KaiPereira/SODIMM-CM5-Carrier/journal/Pasted image 20250924064620.png

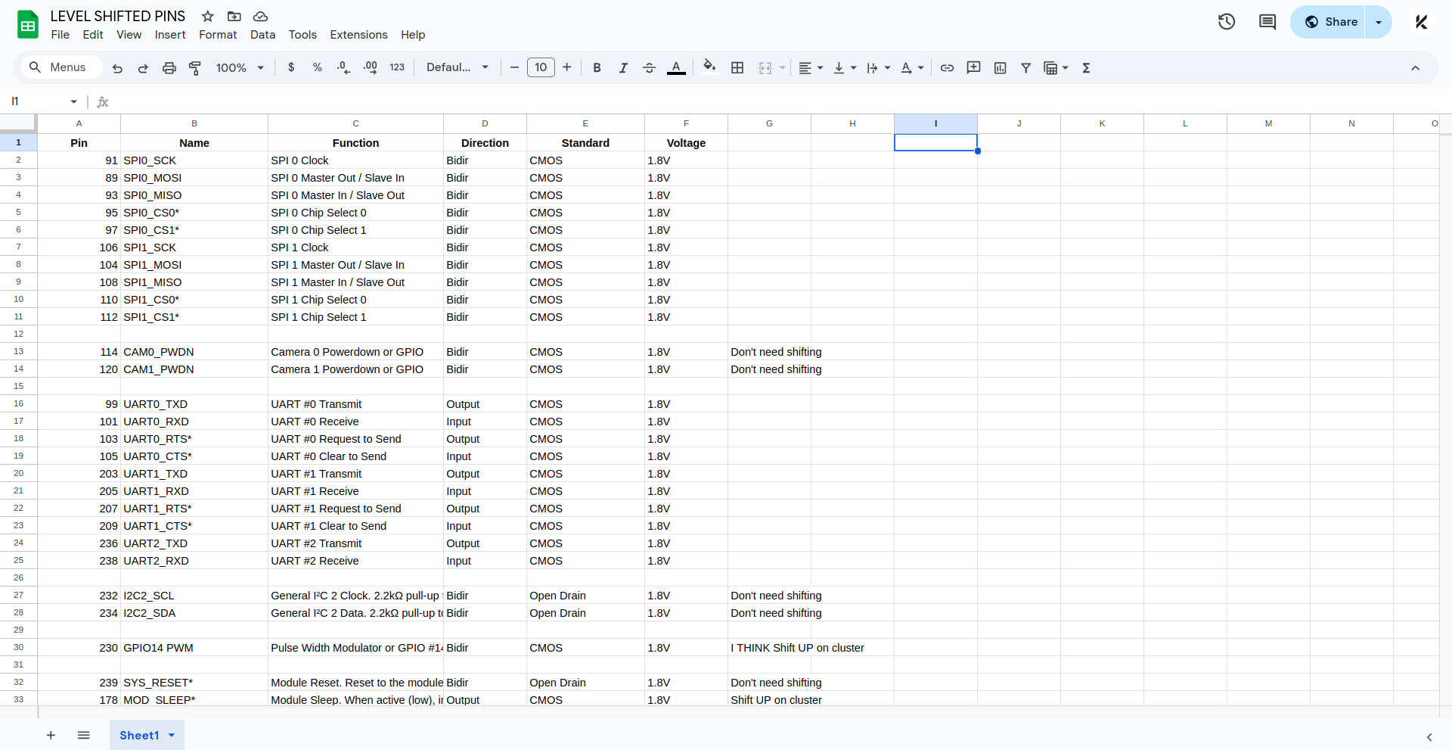
journal/Pasted image 20250924064620.png
