KaiPereira/SODIMM-CM5-Carrier/journal/Pasted image 20251030065639.png

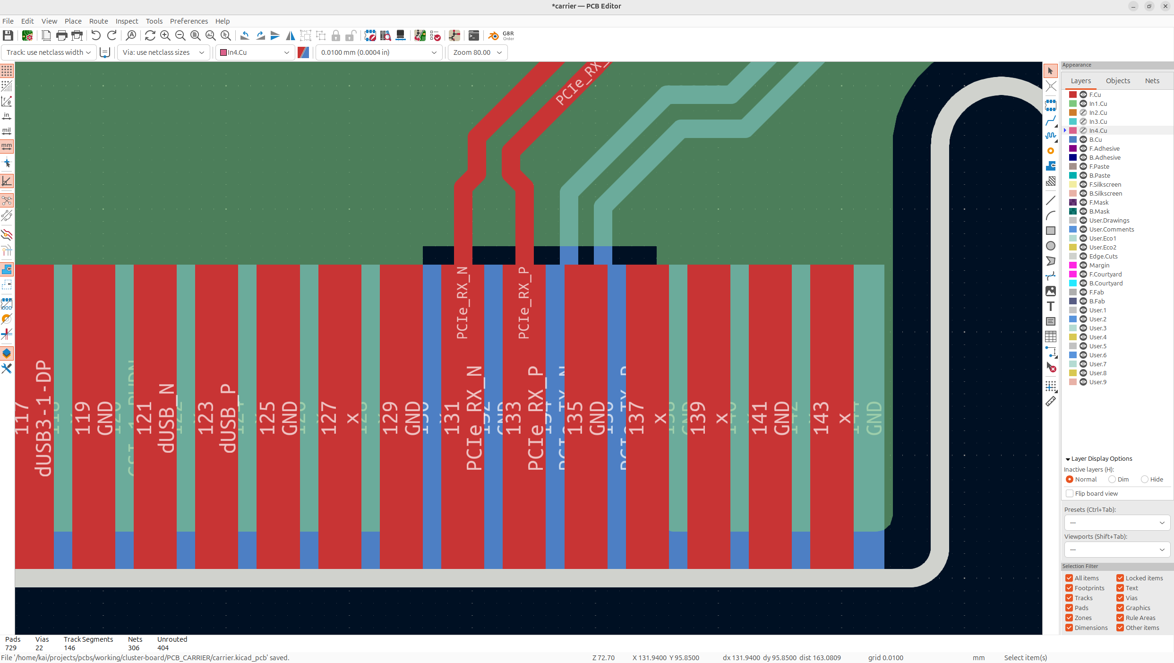
journal/Pasted image 20251030065639.png
